Norman-w/pingpang-smartgear/docs/visual-audit-v0.1.zh-CN.md

# 乒乓智配当前支架可视核验记录 v0.1

本文记录当前 `hardware/cad/net_stand.scad` 的人工可视核验范围和结论。它证明的是 OpenSCAD 装配关系在渲染图中可读，不替代 PETG 实物强度、标准件装配、光学对准或球台现场验收。

## 可复现入口

```text
python3 hardware/cad/render_net_stand_preview.py \
  --output-dir /tmp/pingpang-smartgear-render
python3 hardware/cad/render_m6_views.py \
  --part m6_detector_mount \
  --output-dir /tmp/pingpang-smartgear-render/m6-audit
python3 hardware/cad/render_m6_views.py \
  --part m6_detector_exploded \
  --output-dir /tmp/pingpang-smartgear-render/m6-audit
python3 hardware/cad/export_m6_component_previews.py \
  --clean \
  --output-dir /tmp/pingpang-smartgear-render/m6-component-previews
```

CI 也会在 `OpenSCAD geometry validation` job 中生成并上传当前支架和历史外挂 X 夹具的 PNG artifact。当前支架的渲染脚本输出包括整体装配、左右支架、桌下夹持剖面、斜立柱下段/上段与固定夹体共面落座、立柱与固定基台的爆炸/截面、网布过道与 Ø10 圆柱插杆侧开接收腔爆炸/截面、M6 检测器总成/无剖切爆炸图、M6 各单件、PVDF 座；专用 `render_m6_views.py` 还为总成和爆炸图各输出 x-/x+/y-/y+/z-/z+ 六视图及等轴视图。旧 STG-120ML 托架和标定规仍单独渲染用于历史回归，不作为当前采购件结论。

## 本轮检查项

| 检查对象 | 可视核验内容 | CAD 结论 | 实体验收边界 |
| --- | --- | --- | --- |
| 整体装配 | 左右立柱/桌下夹体、真实网布占位、无网顶轨道、左右各十路 M6 直角对射器件、10×56×216 mm PETG 主体、后盖 x 背面中央加厚 boss、前后盖、底盖、竖直采购球头、PVDF 座和球台截面 | 关系可读；左右各 10 枚器件按 20 mm 单列节距装入主体，左侧发射光轴沿 +x、右侧接收端面朝 −x；采购球头上端 1/4-20 外牙从各自 x 后端进入背面中央 boss，下端 M8×1.25 外牙 z− 进入固定网柱上段中心攻丝座；斜立柱下段从黄灰交界 `z=16 mm` 到分型面 `z=230.5 mm`，上段到 `z=260.5 mm`，两段与固定 C 夹分体打印并由四枚普通盘头/低矮圆头 M3×40 连接，网布/圆柱功能区到 `z=168.5 mm` | 网布厚度/张力、立柱平行度、网顶实测高度、M6 器件实际光学中心、线缆净空、M8 攻丝/嵌件啮合、球头锁紧保持性和 NPN 输出仍待实物 |
| 桌下夹持剖面 | 上下 14 mm 结构夹臂跨台边、上表面可替换保护垫、台底独立压块、加长圆头 M8 螺杆、固定下臂螺母、18 齿圆角锯齿旋钮内两枚对锁螺母、外侧 y 全深实心桥体和渐变下部支撑 | 上保护垫位于桌面与固定上夹板之间；螺杆和台底压块均位于台面底面以下，不需要桌面孔；夹持开口和压块/螺杆区域保留，开口之外的灰色结构沿 y 全深，非接触区为实心桥体，下部支撑靠台侧厚 `40 mm`、外侧收口为 `14 mm` 并形成斜底；固定夹体仅保留连续实心承托和功能开口，当前无独立公母燕尾、钢球/压簧咯噔件或 M4 滑脱件；旋钮对锁叠层和圆角锯齿外圈共同承担手拧驱动；当前 CAD 外轮廓相对台边名义外伸 `156 mm`，满足项目下限 `130 mm`，并与立柱底部共面落座 | 夹紧力、滑移、保护垫压缩/压痕、加长螺杆行程、旋钮握持手感、对锁防松、实心桥体/渐变支撑层间强度和标准件实际装配仍待实物 |
| 斜立柱分段落座与网杆 | `post_clamp_carrier_lower`、`post_clamp_carrier_upper`、固定 C 夹最高承托面、主体 y 向 `3 mm` 网布过道、x 侧开圆柱接收腔 | 下段从黄灰交界 `z=16 mm` 起到分型面 `z=230.5 mm`，上段覆盖 `z=230.5…260.5 mm`；下段包含网布门洞、Ø10 圆柱插杆的侧开接收腔、公键和 Ø2.4×10 mm 导向盲孔，上段包含母槽、四个 Ø3.4 mm 通孔和中心 Ø6.8 mm M8 攻丝底孔，球头下端 M8×1.25 直接进入该座，四枚普通盘头/低矮圆头 `M3×40` 只连接这两个立柱段；两段装好后与 C 形座共面且不向下插入；网布先穿过过道并把空心边套套在圆柱插杆上，再沿 x 推入接收腔，安装上段后封住入口；网布/圆柱功能区为 `z=16…168.5 mm` | 打印配合间隙、分型面定位、共面落座稳定性、M3 啮合深度、M8 攻丝/嵌件、抗扭、层间强度、侧开接收腔防脱行程、圆柱推入力和倾斜仍待实物 |
| 网顶 | 网布连续通过两侧立柱；无轨道、拼接片和承托座 | 网布过道、Ø10 圆柱插杆、侧开接收腔和上段封口关系可读 | 网布白边固定、厚度、张力、插杆防脱和长期变形仍待实物 |
| M6 光电阵列、壳体与直连承力边界 | 左右各一根 10×56×216 mm PETG 长条主体，后盖 x 背面中央加厚 boss，x− 正球弧前盖、x+ 接驳边直角且后部两角圆角的后盖、底盖、10 个单列通道和竖直采购球头 | 主体包络、前后盖分型、boss 的 x 向 Ø7.0 1/4-20 外牙通孔与隐藏螺母、boss 根部 y± 实体桥接肋、底盖线缆孔和球头上端接口可读；球头下端 M8×1.25 进入上段中心攻丝座，斜立柱由 `z=16…230.5 mm` 下段和 `z=230.5…260.5 mm` 上段组成，网布/圆柱功能区为 `z=16…168.5 mm` | 实物螺纹/嵌件、光学中心、发射/接收方向、线缆弯曲、环境光、邻道串扰、球头锁紧保持性和逐通道对准仍待接板 |
| PVDF 座 | 网端座体、可拆薄膜、两侧压片和网布白边/立柱的相对位置 | 薄膜没有被永久并入打印本体，压片关系可读；座体不形成网顶轨道 | 贴合预紧、AFE 波形、机械误报和阈值仍待接板 |
| 高度通道与历史标定规 | 当前 M6 原始 `+10…+190 mm`、总成上抬 20 mm 后 `+30…+210 mm`、`20 mm` 节距的十路单列通道；另保留 STG-120ML 3.87 mm 标定规历史渲染 | 当前只验证通道高度/装配关系；历史标定规不作为 M6 精度依据，也不宣称 NPN 已经接入主控 | 真实光轴高度、球体遮挡宽度、读数误差、NPN 电平转换和校准版本仍待实物 |

## 结论边界

- 当前 CAD 的装配方向、镜像关系、免打孔夹持路径、M6 x 轴光学方向、20 mm 十路 PETG 主体、前后盖分体和后盖 boss/采购球头接口已通过可视核验及自动几何回归。
- M6 总成爆炸图使用完整实体，不使用剖切；“前盖更大且遮住激光头/单枚螺帽”的结论只针对当前 CAD 包络，仍须按真实 SKU 首件复核。
- 后盖 boss 在 STL 中以 `Ø7.0 mm` x 向 1/4-20 外牙通孔和隐藏捕获螺母窝表示，boss 根部另以 y± 两条避开中央孔的实体桥接肋连接到后壳侧壁；实际螺纹/金属承力件由采购球头与标准螺母提供；斜立柱下段/上段的分型面连接、四个 M3 孔和上段中心 `Ø6.8 mm` M8 攻丝底孔分别保留在对应打印件中；主体、前后盖和底盖都是 PETG 首样候选，后续主体/boss 可改 CNC 或加金属嵌件。
- 独立组件导出包包含左右各一套主体、前盖、后盖、底盖，共 8 个完整 STL；正式网架打印包另含左右各一根 Ø10×152.5 mm `net_clamp_rod`，平放打印后沿原门洞轴线从 x 侧装入下段侧开接收腔；采购球头、网布和标准金属件不进入打印 STL。M6 总成和无剖切爆炸图各有 7 张视图（六视图 + 等轴），方向箭头为审计叠加，不进入零件 STL。
- 渲染图不能证明支架在目标球台上夹得住，也不能证明 PVDF 或红外光栅已经有有效电气信号。
- `docs/field-validation-record.example.json` 中的 M/B/S/T/E 现场项目继续保持 `pending`，在没有照片、量具/示波器记录、原始波形和真实事件日志前不改为 `pass`。
