Norman-w/pingpang-smartgear/docs/laser-micro-mount-v0.1.zh-CN.md

# 裸激光可调小夹座 v0.1

左侧发射端用十颗独立小夹座替换固定 M6 发射头，保留20 mm通道间距、后盖球头接口和网架安装基准。两端前盖及底盖同步扩大，接收端另有[配套外壳说明](receiver-mount-v0.1.zh-CN.md)。右侧内部接收元件暂保留原模型作接口参考；本次不把原 M6 接收板当成已兼容裸激光的电路。

本次修正：**调整9号时，10号保持安装；前后盖、底盖和球头也保持固定。** 旧版只检查了零件转动，遗漏了工具通道。新版在夹座下侧梁和承载条后沿切出让位槽，后盖增加 A1–A10、B1–B10 编号入口。1–9号从两侧进入，10号从顶部进入。

前盖修正：旧版矩形内腔将弧形侧壁挖穿，零件“不碰盖子”不代表被完整包住。新版前盖向光学侧加深6 mm，宽度由60.8增至63.6 mm，内腔沿外轮廓向内偏置2.4 mm。前盖外包络为 **24 × 63.6 × 222 mm**。承载条、安装耳和螺钉在弧形前腔内保留至少0.5 mm名义余量。底盖与柔性垫跟随新轮廓扩大；旧底盖不适配。

## 机械契约

- 尺寸暂按铜壳 **Ø6 × 12 mm**，不是已确认的采购规格。`laser_module_d`、`laser_module_length` 是入口参数；当前夹筒允许到 Ø6.2、长15 mm，超过后需要联动放大夹座，不能只缩放 STL。
- 上下夹座、夹筒、承载条、前后盖按 FDM PETG 首样设计；球面衬垫为上下两片 TPU。底部弹簧、螺钉和螺母均为采购金属件，STL 中的金属件只供装配核对。
- 单颗局部坐标的出光方向为 x−，前支点在原点；右侧标准坐标镜像到左侧后，出光朝球台中心 x+。夹座沿 z=0 拆成上下两半。夹筒后口在 x+，裸头从后口插入，前面的小孔是限位肩，不能从前孔硬塞。
- 球面夹筒夹在 TPU 衬垫中，尾部同时抵住两颗斜45°的 M2 微调螺钉；下方金属弹簧把尾部向上推。A/B 同向位移主要调整俯仰，差动主要调整偏航。有限转角有耦合，网页按圆柱与螺钉轴交点计算位置，不把螺钉当成两个完全独立的角度旋钮。
- 裸头的轴向防退由前端护套和后段反侧短顶丝共同完成。后段顶丝是约 Ø3.4、长3 mm 的 M3 级平头机米螺丝，从夹筒尾部外侧向内顶在铜壳后段；凸台内缘距 Ø6 mm 裸头包络保留0.3 mm 名义间隙，不阻挡从 x+ 后口插入。凸台首样预留 Ø2.5 mm M3 攻牙底孔，打印后攻牙；若需要反复维护，改装 M3 热熔螺母。顶丝零位保留约0.05 mm名义间隙，装配时只拧到刚好接触并用低扭矩锁住；它不能代替前限位肩，也不能顶光学镜片或线脚。
- 尾部另加一只独立打印的粗牙空心防脱挡环：C 夹后部做成与主体连通的内螺纹座，挡环从 x+ 方向拧入；螺距2.0 mm、牙根带1.0 mm、锥形牙尖0.45 mm、32段/圈，外螺纹大径16.2 mm，内螺纹座有效大径18.0 mm，挡环后法兰 Ø19.2 × 2.8 mm。法兰外缘加 17 mm 对边六面受力界面，可用薄口扳手或自制叉形工具拧紧，不能把螺纹当作唯一受力点；手拧只用于就位。挡环前端 Ø10.4 mm 捕获孔只让 Ø8.4 mm 尾段通过，在 x=13.8 mm 的台阶面承住 Ø10.6 mm 载筒肩；中心孔贯穿法兰给尾线留出通道。该粗牙比例按 X1C 类 FDM 首样设计，挡环建议沿 x 轴竖直、法兰朝下打印；螺纹可拧合是几何首样结论，仍需按实际层高、材料和首层膨胀试拧。
- 夹座两侧 M2.5 螺钉从光学侧进入，承载条后面放捕获螺母。载荷经两侧安装耳传到承载条连续侧梁，再经头套、球头进入立柱。夹座合拢螺钉从 z+ 进入，底部捕获 M2 螺母；调节轴有内侧防转螺母和外侧锁母。
- 每颗检查范围为上下、左右各 ±3°。主框高度18 mm，零位含金属件的总包络约 **23.5 × 48 × 18.334 mm**；STL 保留装配坐标，未归一化到打印床。
- 原盖件固定孔在第一/最后通道附近，会削弱新开口边缘；因此裸激光版前后盖和承载条配套改用上下端部固定孔。新孔距承载条端面5 mm。加大前盖含平面沉头座和向承载条延伸的支撑，沉头座附近有足够材料承托头部，支撑在接近首尾夹座前变窄。前盖以两颗M3×30沉头螺钉固定，承载条背面装捕获M3螺母；前盖螺钉位于y=0中线，避开10号A/B工具路线。新承载条、前后盖、底盖与底部柔性垫必须成套使用。
- 前盖从光学侧沿光轴推入；承载条上的前盖导槽已向光学侧开口。不要再从顶部下滑，端部支撑会扫过中间夹座。后盖保留原安装方式；底盖从下方合上。前盖支撑到承载条留0.6 mm间隙，螺钉完成固定，原后盖及球头承担整排安装载荷。
- 工具通道沿 A/B 轴线贯通，直径7 mm。夹座侧梁向内加宽到4.5 mm后再切让位槽；承载条只切除后沿最多1.5 mm，连续侧梁保留前侧8.5 mm厚度。调节孔不穿过后盖球头座或它的加强筋。分型、安装耳及弹簧承力位置保持原基准。
- 不承诺密封、定位精度或长期耐久。TPU 外径相对刚性座有0.1 mm直径预紧占位；必须按实际打印材料、层高和铜壳尺寸试配。

## 装配与调整

1. 将限位顶丝螺母装入夹筒，从 x+ 后口插入裸头到前限位肩，轻锁正侧限位顶丝，再轻锁后段反侧短顶丝；两颗都只做防退预压，避免压坏铜壳或改变内部光轴。后端保留软线余量，线束不应给夹筒施加扭力。
2. 在下夹座内放下半衬垫及弹簧，放入球面夹筒，再放上半衬垫、上夹座与合拢螺钉。调节螺母从后侧开口装入。先验证球面能平顺转动且没有明显旷量。
3. 将小夹座固定到承载条，装入前盖螺钉的捕获螺母。前盖从光学侧沿光轴推入并拧好两颗沉头螺钉，再装后盖和配套底盖。用原球头把整排光点大致对上并锁住。随后保持邻近通道和盖件安装，按孔旁 A/B 编号找到目标通道。10号的两孔位于顶部；其余位于侧面，入口比对应光轴高30.4 mm，不能仅按光头高度猜入口。
4. 工具约束：锁母用 **对边4 mm、外径≤6 mm、有效长度≥60 mm的贯通薄壁金属套筒**，1 mm内六角从套筒中心通过。松开锁母、转动内六角微调；再保持内六角不转，用套筒锁紧锁母并复核光点。普通实心柄套筒不能同时穿入内六角。模型按工具手柄转动包络Ø22 mm、长度40 mm检查；采购工具的外径、贯通孔及握持方式仍要核对。
5. 至少检查低、中、高三个通道，并重复拆装、锁紧、轻振动和静置测试。接收侧记录模拟量的余量及触发边沿；软件几何检查不能替代光路和电路实测。
6. 裸头引线先向后引到局部 x≥18 mm再汇入线束；在图示工具通道周围留出余量。软线尚未建模，装线后需重复工具进出测试。网页“拆开查看”和局部剖看只用于说明，不代表调整时拆盖或拆光头。

两颗相邻夹座建议先打印一组试装，用实际工具复核：能插到底、能同时持住内六角并转动套筒、工具可退出、邻居光点不因触碰而移动。随后再打印整排。带工具孔的外壳没有密封设计。

## 单颗物料参考

| 零件 | 数量 | 说明 |
|---|---:|---|
| PETG 下夹座、上夹座、球面夹筒 | 各1 | 独立打印 |
| TPU 上下球面衬垫 | 各1 | 配合量待试片 |
| 裸激光头 | 1 | Ø6×12 mm 占位；按实物确认驱动方式 |
| M2×8 调节顶丝 | 2 | 模型省略螺纹牙形，留内六角入口 |
| M2 螺母 | 7 | 调节防转2、锁母2、合拢2、限位顶丝1 |
| M2×12 合拢螺钉 | 2 | 圆柱头沉孔从上方进入 |
| M2×5 裸头限位顶丝 | 1 | 后期按铜壳夹持要求确认 |
| M3×3 后段反侧短顶丝 | 1 | 平头机米螺丝；Ø2.5 首样底孔攻牙或装 M3 热熔螺母；低扭矩压住铜壳后段 |
| PETG 尾部粗牙空心防脱挡环 | 1 | 外螺纹大径16.2、2 mm螺距、Ø19.2法兰、17 mm对边受力面；沿x轴竖直打印，法兰朝下 |
| M2.5×8 安装螺钉与螺母 | 各2 | 安装耳连接承载条 |
| 压缩弹簧 | 1 | 图示 OD3.2、线径0.4、约3圈仅为包络；刚度、自由长和工作预紧力需选型 |

十路另加一根承载条、新前盖、新后盖、加大底盖与底部柔性垫；前盖另需两颗M3×30沉头螺钉及两颗M3螺母，出线环沿用原接口。省下的是工业光头的安装壳、逐路支架与加工费用；小件装配、弹簧选型和标定仍有成本。本版没有引用未经核实的物料单价。

## 预览与导出

- 主预览页：`hardware/cad/preview/?view=laser`。默认展示9号原位调整：上下邻居保留，可切换1–10号及A/B侧，拖动工具插拔、切换外壳透明度。“单颗结构”保留角度滑块、分离展示、四个视角和零件高亮。
- 两处三维预览均采用正交相机：滚轮围绕鼠标位置缩放，中键/右键拖动平移；也可点“平移”后使用左键拖动。放大不再把相机挤向旋转中心，近处继续缩放和拖动时保持正常响应。视角/归零按钮恢复取景。
- 点击“查看整排安装关系”，进入带完整头套的左侧十路夹座；“隐藏左侧头套”只供看内部，实际调节不需要拆盖。全局按钮恢复整体装配。
- 关闭“左侧使用裸激光可调夹座”可查看原 M6 模型。旧33件打印拼盘仍属于网架通用件与原 M6 方案；新夹座有独立包，不能将两个方案的左侧承载条与盖件重复打印安装。
- 权威来源：`hardware/cad/net_stand.scad` 包含 `laser_micro_mount.scad`。整体装配的左侧默认启用裸激光版本；`-D bare_laser_enabled=false` 可恢复原 M6 组合。

```sh
python3 hardware/cad/export_laser_micro_mount.py
python3 hardware/cad/validate_laser_micro_mount.py
```

独立包：`hardware/cad/exports/laser-micro-mount-v0.1/`。当前清单包含27个零件模型（其中20个单颗夹座/五金条目、7个整排件，11种打印件），另有2个工具展示模型。工具模型不属于打印清单。`manifest.json` 记录两个 SCAD 文件及各 STL 的 SHA256，零件的毫米包围盒、体积和封闭性；`scope` 区分单颗件与整排件；`validation.json` 记录本次检查结果。

打印方向建议：下夹座以 z− 底面落床；上夹座翻转后试排；夹筒以 x+ 尾口落床并评估小底面附着；TPU 衬垫优先以分型面落床。长承载条可沿长度平放；盖件按开放面、槽和支撑的可清理性试排。螺母槽、球面座和悬伸孔仍需切片检查，不把流形检查当作无需支撑的证明。

## 检查范围

对所有输出检查封闭性和非零体积，对10种打印件检查没有漂浮的独立实体。SCAD 检查九组角度组合：俯仰与偏航各取 −3°、0°、+3°；覆盖夹筒与刚性框、首/中/末夹座完整五金与承载条/头套，以及相邻通道。安装耳与承载条的共面接触体积为零，允许接触；任何正体积刚性穿透判失败。

前盖另有三类检查：实际STL在9条剖面射线上都具有完整前壁；前腔中的零件在九组姿态下均落在向内再缩0.5 mm的腔体内；前盖沿光轴从0到50 mm的7个抽出位置均无刚体碰撞。装盖检查为离散位置及导槽几何检查，不包含实物弹性和打印毛刺。

工具检查为10通道 × A/B两侧 × 九组角度，共 **180个情形**：用完整Ø6 mm套筒及Ø22 mm手柄的包络，检查插入位置、向外退出60 mm和整周转动，所有邻居、承载条、盖件与球头均保留。目标螺钉/锁母与工具的接合另用带贯通孔的真实工具模型检查。旧侧梁作为反例仍须被同一工具探针检出阻挡，防止探针放错位置却全部通过。通道名义径向余量为0.5 mm，不等于打印精度。

TPU 预紧、标准件螺纹包络和弹簧弹性变形不纳入刚体穿透判定。软线、实际工具公差、人手和安装现场的外部空间尚未建模。另按2 mm光束和前盖Ø6.6孔检查几何通光余量。以上均是设计验证；尚未做实体打印、铜壳适配、锁紧漂移或电气响应测试。
