Norman-w/pingpang-smartgear/hardware/cad/preview/index.html

配

乒乓智配 / CAD 工程预览

# 网架装配、爆炸与打印检查 · v0.1

正在读取打印清单…

装配 / 爆炸 / 拼盘

## 网架首样 看清楚再打印

这是一套替换传统球网的网架首样：先确认左右夹台、网顶和 M6 直角十路光电阵列怎么装，再拆开检查打印件与采购件，最后进入按材料分盘的打印清单。

装配视图控制

爆炸程度 0%

合并 展开

装配进度 完整 显示球台与球网背景 显示网布、M6 光电器件、线路板、PVDF 和标准件 显示线路板真实 3D 模型 左侧使用裸激光可调夹座 隐藏左侧头套，仅供查看内部 隐藏右侧头套，仅供查看内部

实际调节从 A/B 编号孔进入，头套、邻居和球头保持固定。右侧接收器与驱动电路待单独选型。

接收端已同步加大前盖、底盖及安装接口；内部暂留 M6 接收头参考。接收端零件与说明

显示粗牙 PETG 夹紧件（螺杆/螺母/旋钮）

带“占位”标记的模型来自装配清单，不进入 PETG / TPU 打印拼盘；M6 光电器件、铝合金基座和金属标准件按外购/机加工件处理。

打印床与排版参数

打印机 / 床面预设

宽 X 深 Y 高 Z 边缘余量

零件间距 5 mm ↻ 重新计算排版

材料组严格分盘：PETG 与 TPU/柔性件不会进入同一张打印板；“PETG/TPU 试样”按柔性材料处理。

恢复已生成清单

检查项与导出

显示零件名称 显示边缘余量

视图适配 下载布局 JSON

!

当前有 3 件需要处理

网顶承载条超过当前打印床，源 STL 会保留在清单中，不缩放、不裁切。

通用装配引擎（模板版）↗ 查看源 manifest ↗ STL 单位约定：mm

当前任务 / 打印布局

## STL 打印床排版

—打印床拼盘

—已放置打印件

—超出当前床面

裸激光头 / 独立夹座

查看整排安装关系 查看接收端

打印床俯视 / XY

### 读取中…

—

悬停查看名称，点击查看单件模型

三维装配检查

### 等待选择模型

当前拼盘几何 选中件几何

装配坐标 · mm 悬停或点击三维零件查看中文名称 重点查看

全局 PCB 腔体 UI 面板 立柱/C夹 旋钮加固 M6 阵列 裸激光阵列

电子腔体专页 ↗ M6 右侧近景 方向

等轴 前视 后视 右视 左视 俯视 仰视 平移

坐标：x=光束左右 · y=前后(+y前) · z=竖直(+z上)

◎

选择拼盘或打印件

可旋转、缩放、平移检查 STL 几何

WebGL 3D 预览正在初始化…

装配顺序 / 结构分组

### 按步骤检查网架、M6 阵列和擦网传感器

清除选中

点击三维零件或下方步骤查看对应的中文名称、材料和装配说明。

当前拼盘 / 打印件

### 当前拼盘包含的打印件

打印床边界 / 待处理

### 无法放入当前打印床

—

重新生成实际拼盘文件： python3 hardware/cad/build_print_platter.py --clean

装配物料 / 与打印件分开管理

### 打印前准备的外购件与软质接触件

装配补充清单

元件类别数量处理备注

本页只负责首样 STL 的排版与装配核对，不替代切片器。 切片前确认 1:1 单位、方向、支撑、壁数、填充和首层。
