Norman-w/pingpang-smartgear/hardware/cad/preview/electronics.html

腔

乒乓智配 / 机械电子联合检查

# C 夹电子腔体专页 · 当前方案

正在读取当前 STL 与参数…

C 夹 / 电子腔 / 维护视角

## 把腔体打开 看清板与 内装封口板

这里单独检查右侧主控腔、左侧发射腔和 y+ 侧面的 UI。页面载入正式壳体、一体式外侧齐平 UI 填平固定板（含腔内八孔搭接法兰和捕获环）、包含按键/LED/唯一 Type-C 充电口 KiCad 3D 模型的板级 STL，以及由 SCAD 挂载的屏幕、扬声器等线束实体件。

选择腔体

右侧主控 左侧发射

右侧显示 ESP32 主控板、y+ 侧壁 UI 子板和一体式外侧齐平填平固定板；左侧显示发射电源板。两个腔体通过上方按钮分别查看，不在同一画布叠放。

快速视角

等轴 分型面 y+ 外侧 俯视 底视

适配当前 恢复原位

拆解与壳体

维护展开 0% 壳体透明度 22% 显示操作者侧半体（y−） 显示对手侧半体（y＋）

内部对象

主控板（真实 KiCad STL） 发射电源板（真实 KiCad STL） y+ UI 子板 + 线束实体件 + 内装封口板

主控板与发射板显示为 KiCad 导出的真实板级 STL；UI 板 STL 同时包含 PCB 直装按键、LED、唯一 Type-C 充电口，屏幕/扬声器等线束实体来自 net_stand.scad。

当前对象

未选择对象

鼠标移动到模型上查看名称；点击后固定说明。

← 返回总装配预览 查看当前源 manifest ↗ 坐标：x=光束左右 · y=前后（y+ 为 UI 侧壁）· z=竖直

专用视图 / 电子腔维护

## 壳体、线路板与实体器件

—可视对象

116.8 × 40腔体 XY / mm

物理首样验证仍待做

Three.js 实时装配视图

### 右侧主控电子腔 · 开放腔体

腔体 PCB UI 面板

◎

正在读取当前壳体和电子模型…

可旋转、缩放、平移；建议先用“分型面”视角

世界坐标轴
红 X：左右 · 绿 Y：前后（Y+ UI侧） · 蓝 Z：上下

网页显示用于检查安装关系和维护空间；它不替代切片、装配和首样受力验证。

对象图例

### 颜色只用于区分层级

当前 C 夹半体

主控 / PCB

发射电源板

UI 子板 + KiCad 贴板件

一体式外侧齐平 UI 填平固定板 STL

当前参数基准

### 来自 net_stand.scad

电子腔有效范围116.8 × 40 mm

主控板86 × 32 × 5.84 mm

发射电源板KiCad STL

UI 子板KiCad STL（含按键/LED/唯一 Type-C 充电口）+ SCAD 线束件

一体式 UI 填平固定板外板 62.8 × 32.8 mm + 腔内法兰 72 × 42 mm · 8×2 mm 蘑菇头自攻钉直锁 Ø1.6 内壁盲孔（通孔 Ø2.3，捕获环与面板融合 0.4 mm）
