Norman-w/pingpang-smartgear/hardware/cad/preview/laser-micro.html

独立微调 · 原球头负责整排粗调

# 可调激光夹座

正在读取尺寸…

正在载入夹座 STL…

拖动旋转 · 滚轮缩放

尺寸与导出清单 ↗结构与装配说明 ↗

下载独立打印件

## 邻居和头套保持安装

调节哪一颗

A 侧B 侧

抽出工具 0 mm 头套半透明，查看孔内

正在载入原位调节模型…

1. 球头先完成整排粗调并锁住。
2. 从对应编号的孔伸入工具，调 A / B。
3. 内六角保持顶丝不转，外套筒拧紧锁母。

套筒需为对边 4 mm 的贯通薄壁款，外径 ≤6 mm、有效长度 ≥60 mm；中间穿 1 mm 内六角。先核对实物工具尺寸。

## 试着调整一颗

上下角度 0.0° 左右角度 0.0°

A / B 螺钉位移：0 / 0 mm

拆开查看 0% 上夹座半透明

## 结构怎么起作用

1前端球面支点夹筒转动，光头靠近支点，衬垫由上下夹座夹住。 2两颗斜向微调螺钉A / B 同向调上下，差动调左右；调好后拧紧锁母。 3底部金属弹簧预紧持续把夹筒顶向两颗螺钉，减少松旷。 4独立装入整排裸头由前护套、正侧限位顶丝和后段反侧短顶丝固定，小夹座两侧螺钉连接承载条。

当前为尺寸可修改的首样模型。转角演示不等于实物精度；需实测裸头尺寸、弹簧预紧和锁紧后的光点漂移。
