Norman-w/pingpang-smartgear/vision/README.md

# 视觉识别工程

当前网顶设备首版不使用相机或视觉作为测量主链路。这里保留为未来外部视频回放、时间戳关联和实验对照的可选目录，不参与 `NetEvent v0.1` 的实时判定。

外部海康威视等设备可以依据 `timestamp_us` 对事件做后续回放复核，但其视频结果不回写为首版的连续高度值，也不改变训练/实验用途边界。
