Norman-w/pingpang-smartgear/hardware/cad/preview.png

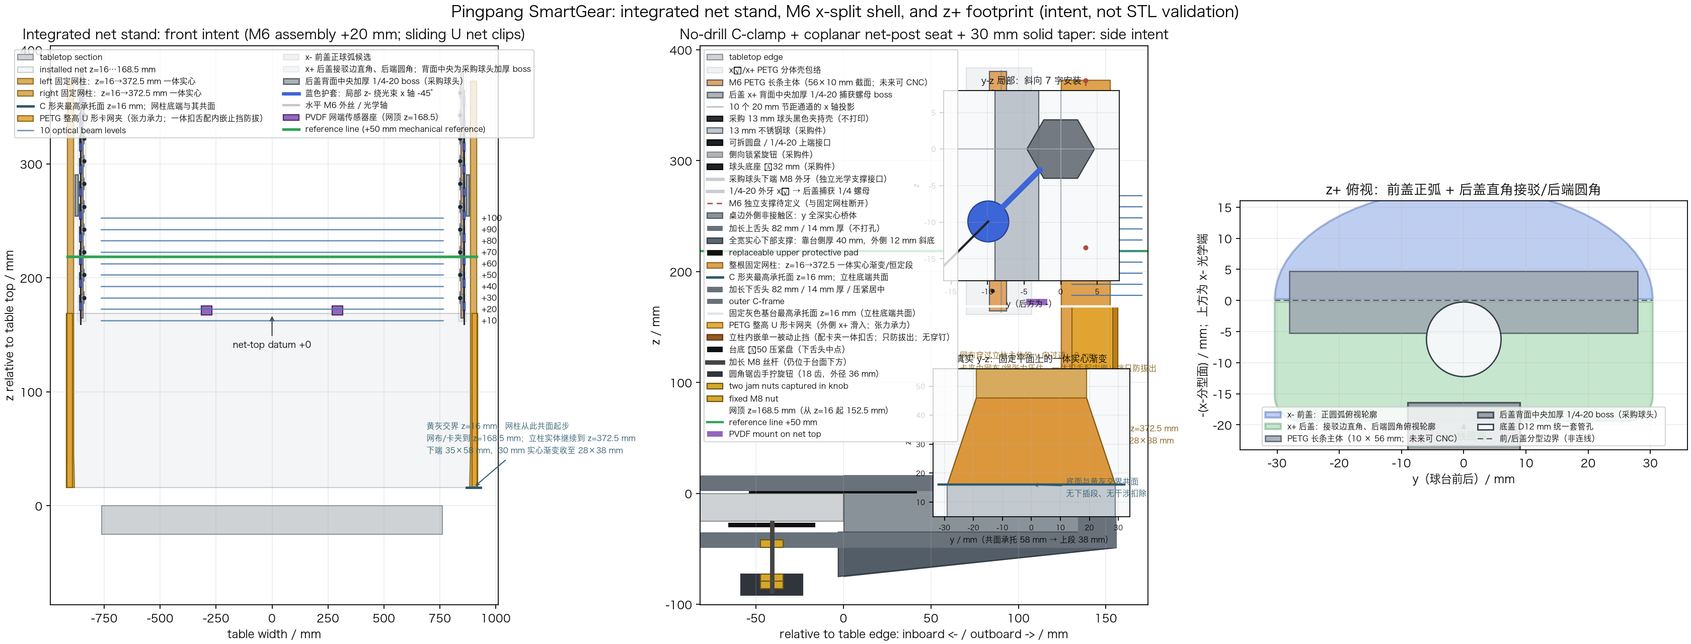
hardware/cad/preview.png
