Norman-w/pingpang-smartgear/hardware/cad/review/electronics-full-cutaway.png

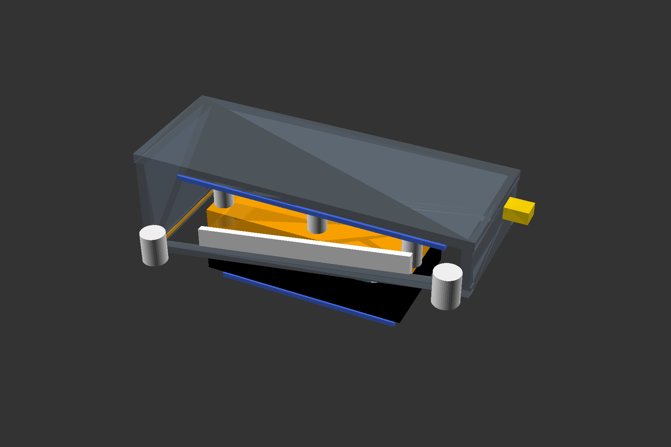
hardware/cad/review/electronics-full-cutaway.png
