Norman-w/pingpang-smartgear/hardware/cad/review/electronics-left-exploded.png

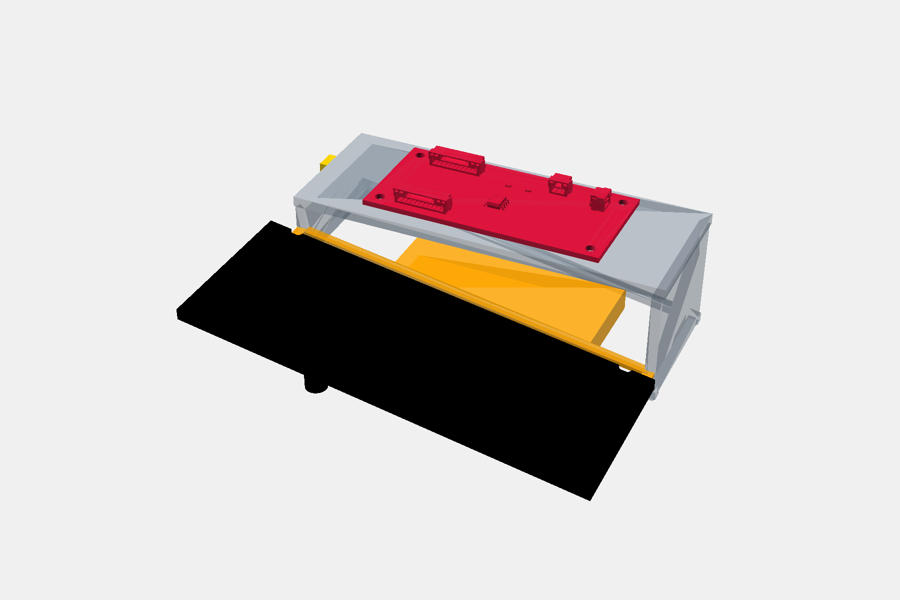
hardware/cad/review/electronics-left-exploded.png
