Norman-w/pingpang-smartgear/hardware/cad/review/electronics-right-exploded-side.png

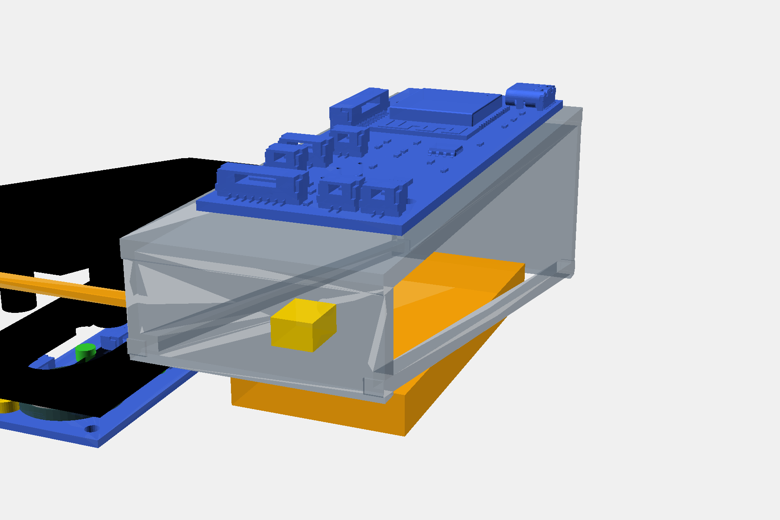
hardware/cad/review/electronics-right-exploded-side.png
