Norman-w/pingpang-smartgear/hardware/cad/review/electronics-right-exploded.png

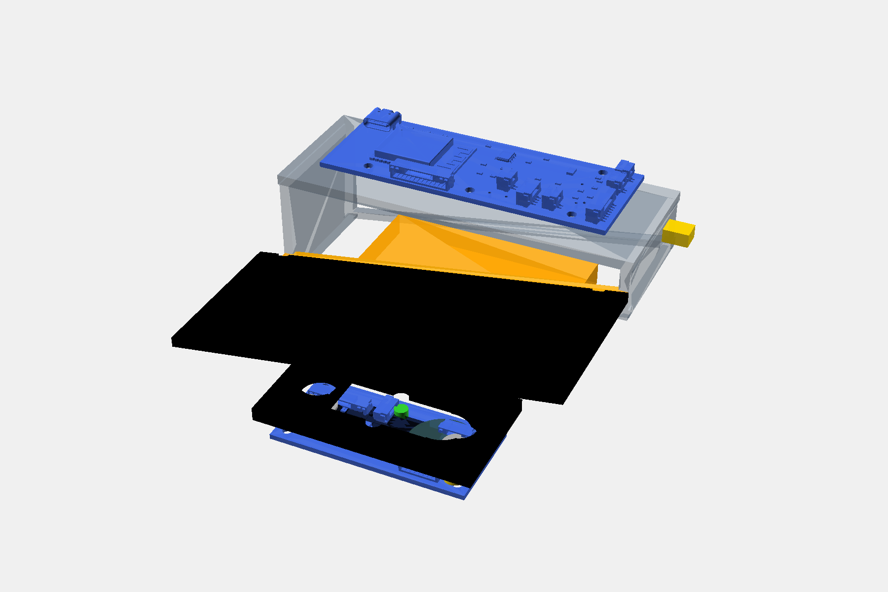
hardware/cad/review/electronics-right-exploded.png
