Norman-w/pingpang-smartgear/hardware/cad/review/m6-receiver-exploded-rear.png

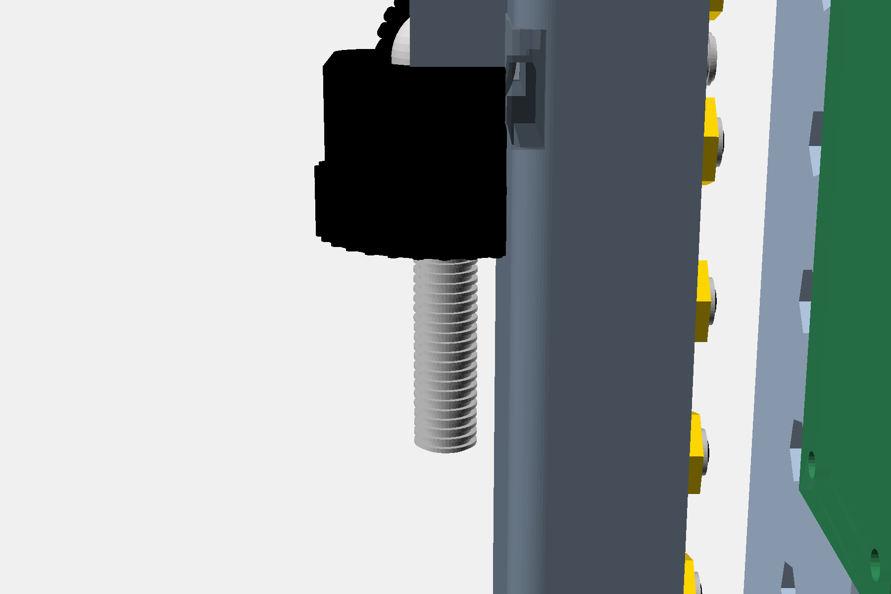
hardware/cad/review/m6-receiver-exploded-rear.png
