Norman-w/pingpang-smartgear/hardware/cad/review/m6-receiver-exploded.png

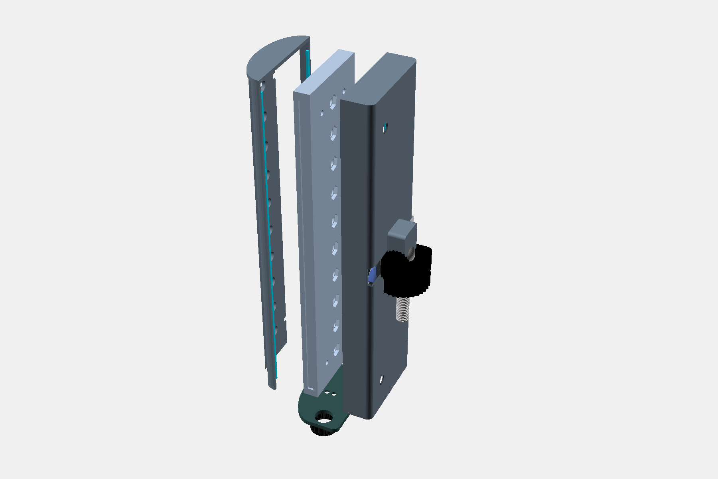
hardware/cad/review/m6-receiver-exploded.png
