Norman-w/pingpang-smartgear/hardware/electronics/daughter-boards-v0.2/emitter-power-v0.2-top.png

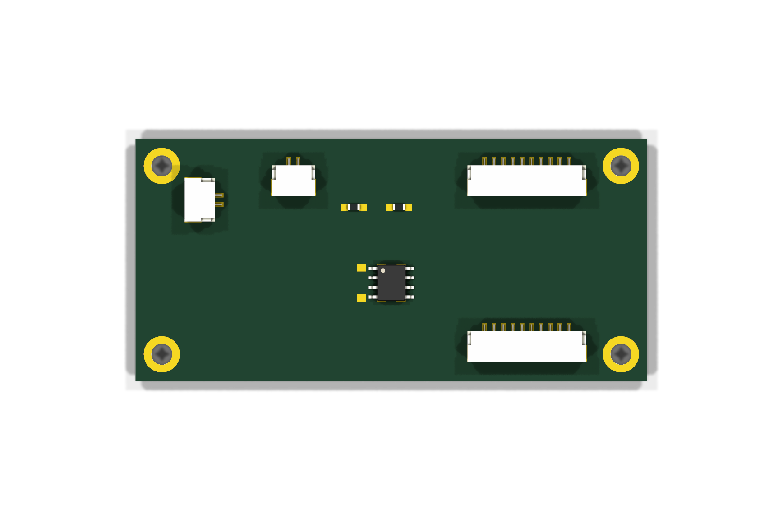
hardware/electronics/daughter-boards-v0.2/emitter-power-v0.2-top.png
