Norman-w/pingpang-smartgear/hardware/electronics/daughter-boards-v0.2/ui-panel-v0.2-top.png

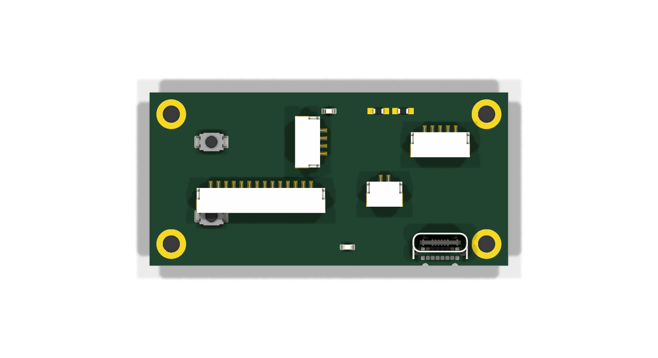
hardware/electronics/daughter-boards-v0.2/ui-panel-v0.2-top.png
