Norman-w/pingpang-smartgear/hardware/cad/review/electronics-emitter-assembly.png

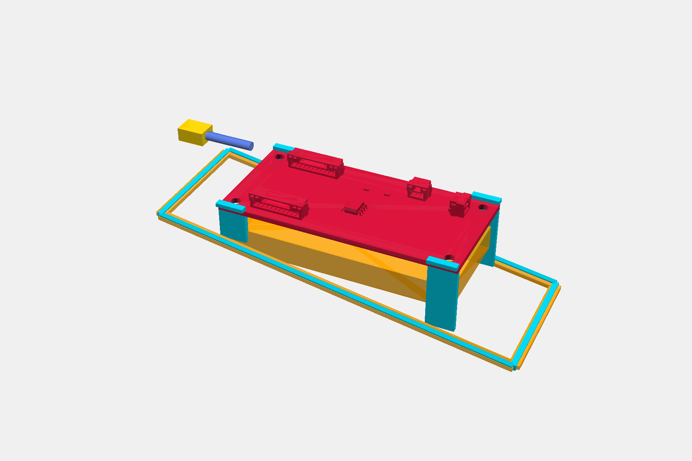
hardware/cad/review/electronics-emitter-assembly.png
