Norman-w/pingpang-smartgear/hardware/cad/review/electronics-ui-assembly.png

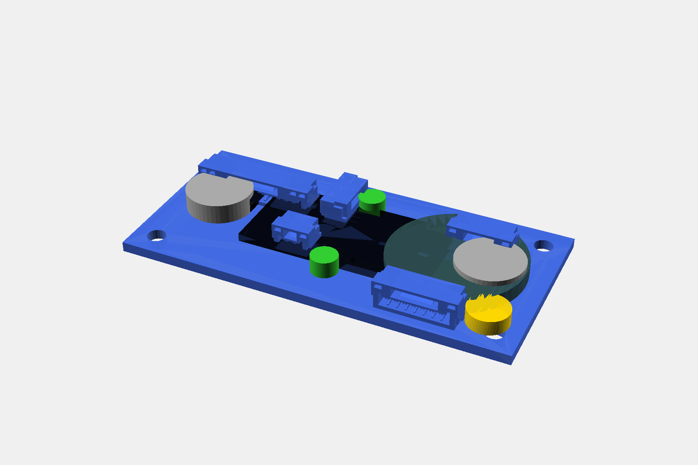
hardware/cad/review/electronics-ui-assembly.png
