Norman-w/pingpang-smartgear/hardware/cad/review/m6-receiver-installed-auto.png

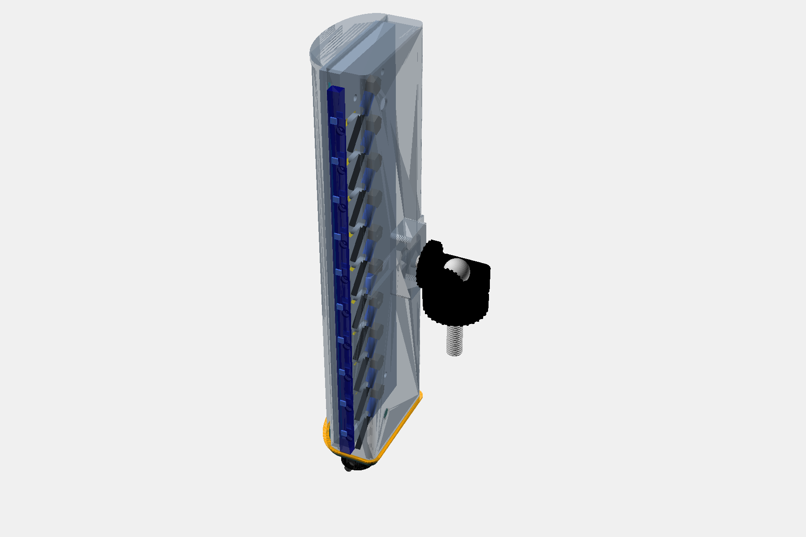
hardware/cad/review/m6-receiver-installed-auto.png
