Norman-w/pingpang-smartgear/hardware/cad/review/m6-receiver-installed-close.png

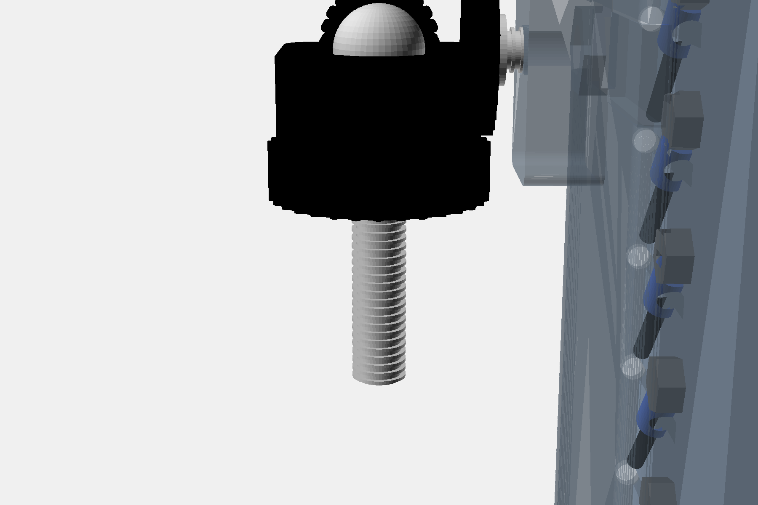
hardware/cad/review/m6-receiver-installed-close.png
