Norman-w/pingpang-smartgear/hardware/cad/review/m6-receiver-installed.png

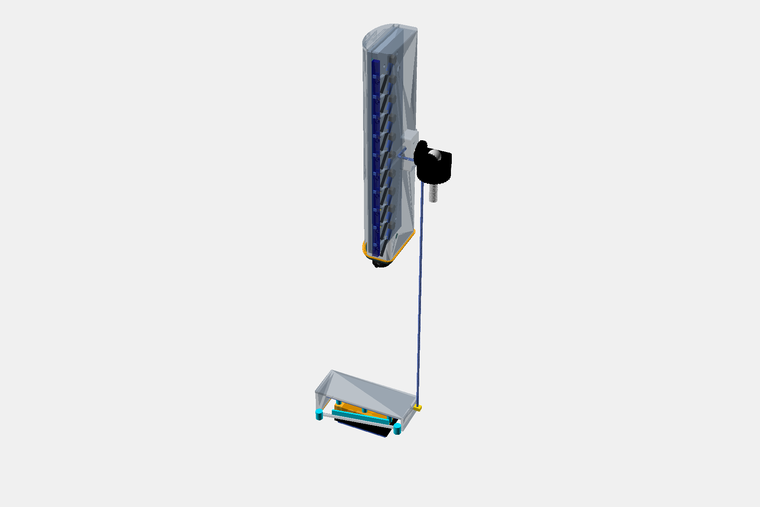
hardware/cad/review/m6-receiver-installed.png
