Norman-w/pingpang-smartgear/firmware/main/piezo_capture.h

#pragma once

#include <array>
#include <cstdint>
#include <optional>
#include <string>

#include "piezo_features.h"

namespace smartgear {

struct PiezoObservation {
    bool valid = false;
    bool triggered = false;
    std::uint8_t sensor_mask = 0;
    std::array<float, 2> peak = {0.0F, 0.0F};
    std::array<float, 2> energy = {0.0F, 0.0F};
    std::uint64_t first_trigger_us = 0;
    std::uint64_t last_trigger_us = 0;
    std::uint64_t duration_us = 0;
    std::string waveform_ref;
    bool features_ready = false;
};

class PiezoCapture {
  public:
    explicit PiezoCapture(std::uint64_t merge_window_us,
                          std::uint64_t waveform_timeout_us);

    // 比较器 ISR/ADC 业务适配器调用此方法；这里不直接操作 GPIO 或 ADC。
    // waveform_ref 为空时只保留候选，不能把它当成已完成波形。
    std::optional<PiezoObservation> on_trigger(
        std::uint8_t channel,
        std::uint64_t timestamp_us,
        float peak,
        float energy,
        const std::string& waveform_ref);
    void on_waveform_ready(const std::string& waveform_ref,
                           const PiezoFeatureSummary& features);
    // Pure look-ahead used by the runtime before allocating a new ADC frame.
    bool will_start_new_observation(std::uint64_t timestamp_us) const;
    std::optional<PiezoObservation> poll(std::uint64_t timestamp_us);
    void reset();

  private:
    std::optional<PiezoObservation> finish();

    std::uint64_t merge_window_us_;
    std::uint64_t waveform_timeout_us_;
    // Preserve the comparator stream boundary across candidate resets so a
    // late edge cannot become a fresh valid touch candidate.
    std::uint64_t stream_last_timestamp_us_ = 0;
    bool stream_has_timestamp_ = false;
    bool pending_ = false;
    PiezoObservation pending_observation_;
};

}  // namespace smartgear
