Norman-w/pingpang-smartgear/firmware/main/piezo_features.h

#pragma once

#include <array>
#include <cstdint>

namespace smartgear {

struct PiezoFeatureSummary {
    std::array<float, 2> peak = {0.0F, 0.0F};
    std::array<float, 2> energy = {0.0F, 0.0F};
    std::uint64_t duration_us = 0;
    // false means a partial frame was retained and the event must remain
    // waveform_incomplete even though partial features are available.
    bool complete = false;
};

}  // namespace smartgear
